fcaspe/bFreeOrgan/src/inc/sine_wave.h

//ARCHIVO GENERADO AUTOMATICAMENTE POR LA UTILIDAD SineGen.
//UTN-frbb 2017 Tecnicas Digitales 3.
//ANCHO DE PALABRA DE FASE: 12 bits
//ANCHO DE PALABRA AMPLTITUD: 12 bits

const int16_t wave_sine[4096] = {

0x0000,0x0003,0x0006,0x0009,0x000C,0x000F,0x0012,0x0015,
0x0019,0x001C,0x001F,0x0022,0x0025,0x0028,0x002B,0x002F,
0x0032,0x0035,0x0038,0x003B,0x003E,0x0041,0x0045,0x0048,
0x004B,0x004E,0x0051,0x0054,0x0057,0x005B,0x005E,0x0061,
0x0064,0x0067,0x006A,0x006D,0x0070,0x0074,0x0077,0x007A,
0x007D,0x0080,0x0083,0x0086,0x008A,0x008D,0x0090,0x0093,
0x0096,0x0099,0x009C,0x009F,0x00A3,0x00A6,0x00A9,0x00AC,
0x00AF,0x00B2,0x00B5,0x00B9,0x00BC,0x00BF,0x00C2,0x00C5,
0x00C8,0x00CB,0x00CE,0x00D2,0x00D5,0x00D8,0x00DB,0x00DE,
0x00E1,0x00E4,0x00E7,0x00EA,0x00EE,0x00F1,0x00F4,0x00F7,
0x00FA,0x00FD,0x0100,0x0103,0x0107,0x010A,0x010D,0x0110,
0x0113,0x0116,0x0119,0x011C,0x011F,0x0123,0x0126,0x0129,
0x012C,0x012F,0x0132,0x0135,0x0138,0x013B,0x013E,0x0142,
0x0145,0x0148,0x014B,0x014E,0x0151,0x0154,0x0157,0x015A,
0x015D,0x0161,0x0164,0x0167,0x016A,0x016D,0x0170,0x0173,
0x0176,0x0179,0x017C,0x017F,0x0183,0x0186,0x0189,0x018C,
0x018F,0x0192,0x0195,0x0198,0x019B,0x019E,0x01A1,0x01A4,
0x01A7,0x01AB,0x01AE,0x01B1,0x01B4,0x01B7,0x01BA,0x01BD,
0x01C0,0x01C3,0x01C6,0x01C9,0x01CC,0x01CF,0x01D2,0x01D5,
0x01D8,0x01DC,0x01DF,0x01E2,0x01E5,0x01E8,0x01EB,0x01EE,
0x01F1,0x01F4,0x01F7,0x01FA,0x01FD,0x0200,0x0203,0x0206,
0x0209,0x020C,0x020F,0x0212,0x0215,0x0218,0x021B,0x021E,
0x0221,0x0224,0x0227,0x022B,0x022E,0x0231,0x0234,0x0237,
0x023A,0x023D,0x0240,0x0243,0x0246,0x0249,0x024C,0x024F,
0x0252,0x0255,0x0258,0x025B,0x025E,0x0261,0x0264,0x0267,
0x026A,0x026D,0x0270,0x0273,0x0276,0x0279,0x027C,0x027F,
0x0282,0x0285,0x0288,0x028B,0x028E,0x0290,0x0293,0x0296,
0x0299,0x029C,0x029F,0x02A2,0x02A5,0x02A8,0x02AB,0x02AE,
0x02B1,0x02B4,0x02B7,0x02BA,0x02BD,0x02C0,0x02C3,0x02C6,
0x02C9,0x02CC,0x02CF,0x02D2,0x02D4,0x02D7,0x02DA,0x02DD,
0x02E0,0x02E3,0x02E6,0x02E9,0x02EC,0x02EF,0x02F2,0x02F5,
0x02F8,0x02FA,0x02FD,0x0300,0x0303,0x0306,0x0309,0x030C,
0x030F,0x0312,0x0315,0x0318,0x031A,0x031D,0x0320,0x0323,
0x0326,0x0329,0x032C,0x032F,0x0332,0x0334,0x0337,0x033A,
0x033D,0x0340,0x0343,0x0346,0x0348,0x034B,0x034E,0x0351,
0x0354,0x0357,0x035A,0x035C,0x035F,0x0362,0x0365,0x0368,
0x036B,0x036E,0x0370,0x0373,0x0376,0x0379,0x037C,0x037F,
0x0381,0x0384,0x0387,0x038A,0x038D,0x038F,0x0392,0x0395,
0x0398,0x039B,0x039D,0x03A0,0x03A3,0x03A6,0x03A9,0x03AB,
0x03AE,0x03B1,0x03B4,0x03B7,0x03B9,0x03BC,0x03BF,0x03C2,
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
