fcaspe/bFreeOrgan/src/inc/calibration.h

/*ARCHIVO GENERADO AUTOMATICAMENTE POR LA UTILIDAD NOTECALC.
UTN-frbb 2017 Tecnicas Digitales 3.

-- TABLA DE SALTOS FRACCIONALES, ORDENADOS POR NUMERO DE NOTA MIDI --

DETALLES DE OPERACION:
FRECUENCA DE MUESTREO: 42000 Hz.
ANCHO DE PALABRA DE TABLA: 12 bits
RESOLUCION FRACCIONAL; 16 bits*/

#define MIDI_NOTE_OFFSET 36 //OFFSET DE LA NOTA MAS BAJA DEL TECLADO DE NUESTRO ORGANO

const q12q16_t qstep[79] = {
0x000660F1,0x0006C20B,0x000728EA,0x000795E8,0x00080961,0x000883B7,0x00090554,0x00098EA6,
0x000A2022,0x000ABA45,0x000B5D92,0x000C0A96,0x000CC1E2,0x000D8415,0x000E51D5,0x000F2BD0,
0x001012C2,0x0011076F,0x00120AA8,0x00131D4C,0x00144045,0x0015748A,0x0016BB25,0x0018152B,
0x001983C5,0x001B082B,0x001CA3AA,0x001E57A0,0x00202583,0x00220EDE,0x00241551,0x00263A98,
0x00288089,0x002AE915,0x002D764A,0x00302A56,0x0033078A,0x00361056,0x00394753,0x003CAF40,
0x00404B07,0x00441DBB,0x00482AA2,0x004C7531,0x00510113,0x0055D22A,0x005AEC94,0x006054AD,
0x00660F13,0x006C20AC,0x00728EA6,0x00795E81,0x0080960D,0x00883B76,0x00905544,0x0098EA62,
0x00A20226,0x00ABA454,0x00B5D928,0x00C0A95A,0x00CC1E26,0x00D84158,0x00E51D4D,0x00F2BD02,
0x01012C1B,0x011076EC,0x0120AA87,0x0131D4C3,0x0144044B,0x015748A8,0x016BB250,0x018152B3,
0x01983C4D,0x01B082B0,0x01CA3A9A,0x01E57A04,0x02025835,0x0220EDD8,0x0241550E};

/*ARCHIVO GENERADO AUTOMATICAMENTE POR LA UTILIDAD SWITCHBOX.
UTN-frbb 2017 Tecnicas Digitales 3.

-- TABLA DE 9 CONTACTOS POR NOTA MIDI  --

DETALLES DE OPERACION:
NOTA MAS GRAVE 24.NOTA MAS AGUDA: 84.
TOTAL NOTAS: 61.
TONO MINIMO: 24. TONO MAXIMO: 102.
TOTAL GENERADORES DE TONO: 79.
RECORDAR QUE EL ACCESO A LA TABLA SE HACE CON UN OFFSET DE LA MENOR NOTA MIDI SELECCIONADA*/

const uint8_t switchbox[549] = {
0,7,0,12,19,24,28,31,36,
1,8,1,13,20,25,29,32,37,
2,9,2,14,21,26,30,33,38,
3,10,3,15,22,27,31,34,39,
4,11,4,16,23,28,32,35,40,
5,12,5,17,24,29,33,36,41,
6,13,6,18,25,30,34,37,42,
7,14,7,19,26,31,35,38,43,
8,15,8,20,27,32,36,39,44,
9,16,9,21,28,33,37,40,45,
10,17,10,22,29,34,38,41,46,
11,18,11,23,30,35,39,42,47,
0,19,12,24,31,36,40,43,48,
1,20,13,25,32,37,41,44,49,
2,21,14,26,33,38,42,45,50,
3,22,15,27,34,39,43,46,51,
4,23,16,28,35,40,44,47,52,
5,24,17,29,36,41,45,48,53,
6,25,18,30,37,42,46,49,54,
7,26,19,31,38,43,47,50,55,
8,27,20,32,39,44,48,51,56,
9,28,21,33,40,45,49,52,57,
10,29,22,34,41,46,50,53,58,
11,30,23,35,42,47,51,54,59,
12,31,24,36,43,48,52,55,60,
13,32,25,37,44,49,53,56,61,
14,33,26,38,45,50,54,57,62,
15,34,27,39,46,51,55,58,63,
16,35,28,40,47,52,56,59,64,
17,36,29,41,48,53,57,60,65,
18,37,30,42,49,54,58,61,66,
19,38,31,43,50,55,59,62,67,
20,39,32,44,51,56,60,63,68,
21,40,33,45,52,57,61,64,69,
22,41,34,46,53,58,62,65,70,
23,42,35,47,54,59,63,66,71,
24,43,36,48,55,60,64,67,72,
25,44,37,49,56,61,65,68,73,
26,45,38,50,57,62,66,69,74,
27,46,39,51,58,63,67,70,75,
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
